Angeliyuss/Alarma-Magnetica/Diseño 3D/DISEÑO 3D taller de diseño foto 4.png

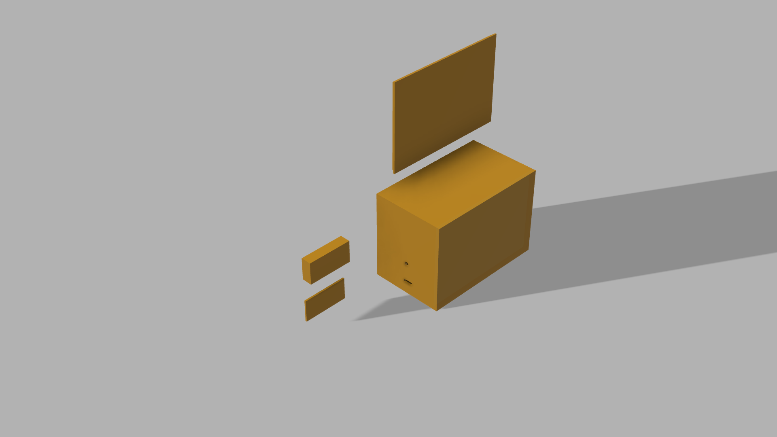
Diseño 3D/DISEÑO 3D taller de diseño foto 4.png
