Angeliyuss/Alarma-Magnetica/hardware/esquema .png

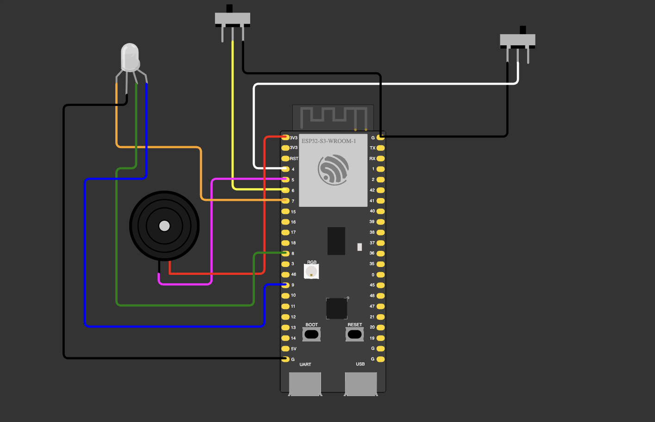
hardware/esquema .png
