Angeliyuss/Alarma-Magnetica/hardware/fotos/Demo.png

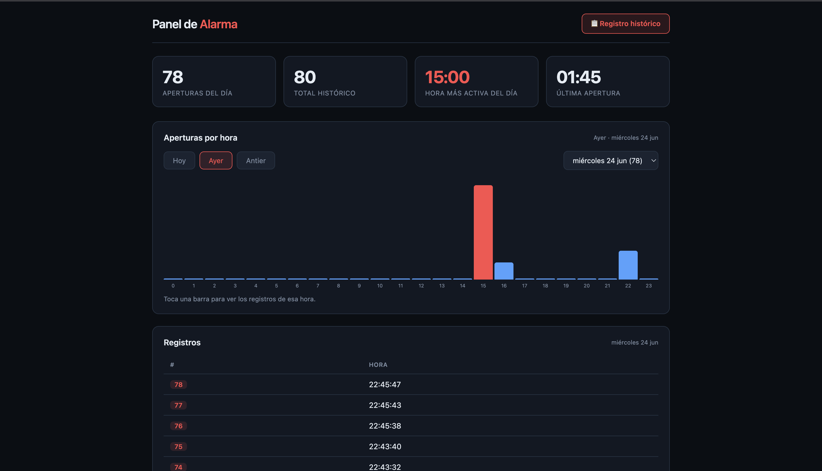
hardware/fotos/Demo.png
